Ali-Mohamed0/ASUMobiCarG30/AVR examples & data sheet/BLINK_AVR.ino

#include <avr/io.h>
#include <avr/delay.h> 
int main(void) { 
  DDRB = 0b00000001;  
while(1)     {
  PORTB = 0b00000001; 
  _delay_ms(500);      
  PORTB = 0b00000000; 
  _delay_ms(500); 
  }
  return 0; 
 }
