Ali-Mohamed0/ASUMobiCarG30/Arduino examples/SHEET_1__EX.1.ino

void setup() {
  // put your setup code here, to run once:
pinMode(1,OUTPUT);
}

void loop() {
  // put your main code here, to run repeatedly:
digitalWrite(1,HIGH);
delay(500);
digitalWrite(1,LOW);
delay(1500);

}
